wenzellabs/flwr/pic/flwr_pcb_kicad.png

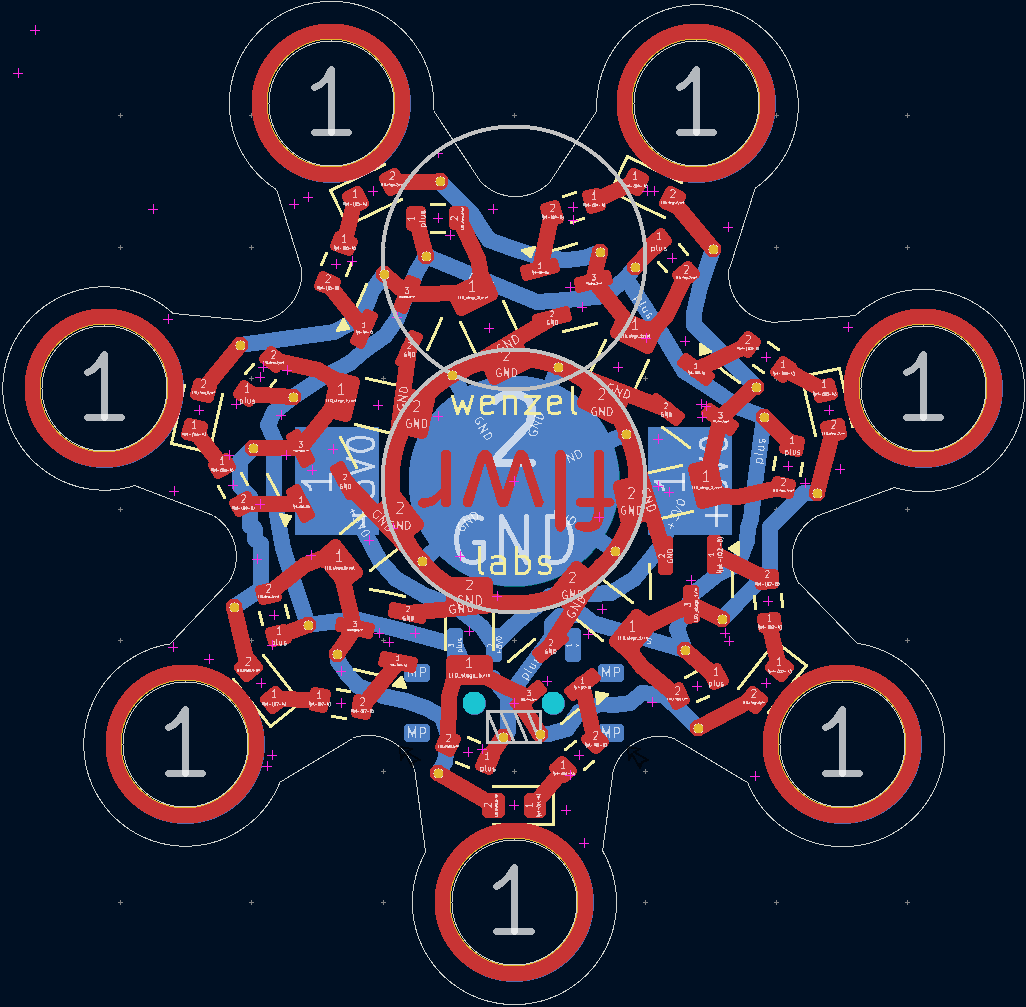
pic/flwr_pcb_kicad.png
