wenzellabs/flwr/pic/flwr_render_back.png

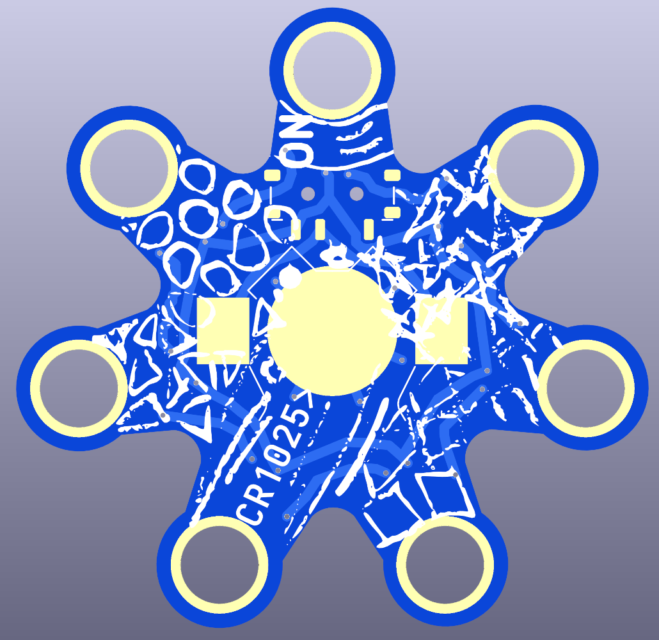
pic/flwr_render_back.png
