wenzellabs/flwr/pic/flwr_render_front.png

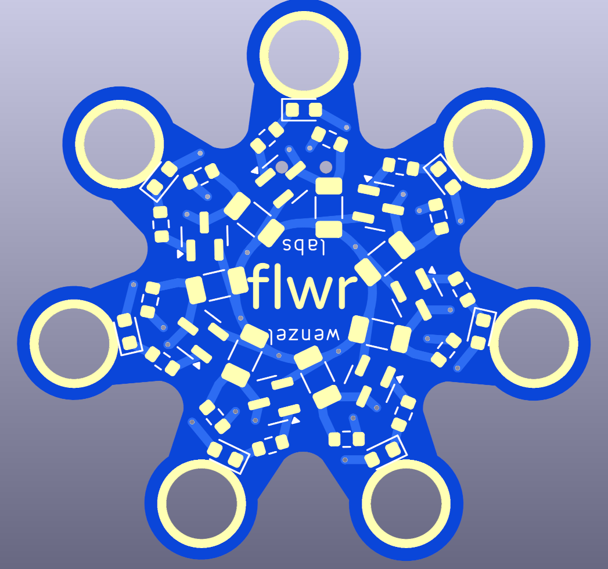
pic/flwr_render_front.png
